bellwood420/pong-arcade-fpga/boards/DE10-NANO/reset_sync.sv

/*
 * Reset synchronizer (Intel/Altera)
 * Assert asynchronously, deassert synchronously
 */
module reset_sync(
  input   logic   clk,
  input   logic   reset,
  output  logic   out
);
  (* altera_attribute = {"-name SYNCHRONIZER_IDENTIFICATION FORCED_IF_ASYNCHRONOUS"} *) logic q1;
  (* altera_attribute = {"-name SYNCHRONIZER_IDENTIFICATION FORCED_IF_ASYNCHRONOUS"} *) logic q2;

  always @(posedge clk, posedge reset) begin
    if (reset) begin
      q1 <= 1'b1;
      q2 <= 1'b1;
    end else begin
      q1 <= 1'b0;
      q2 <= q1;
    end
  end

  assign out = q2;

endmodule
