bellwood420/pong-arcade-fpga/boards/NEXYS4DDR/NEXYS4DDR.srcs/sources_1/ip/mmcm/mmcm_stub.v

// Copyright 1986-2020 Xilinx, Inc. All Rights Reserved.
// --------------------------------------------------------------------------------
// Tool Version: Vivado v.2020.1 (win64) Build 2902540 Wed May 27 19:54:49 MDT 2020
// Date        : Sat Nov 14 17:16:30 2020
// Host        : DESKTOP running 64-bit major release  (build 9200)
// Command     : write_verilog -force -mode synth_stub -rename_top mmcm -prefix
//               mmcm_ mmcm_stub.v
// Design      : mmcm
// Purpose     : Stub declaration of top-level module interface
// Device      : xc7a100tcsg324-1
// --------------------------------------------------------------------------------

// This empty module with port declaration file causes synthesis tools to infer a black box for IP.
// The synthesis directives are for Synopsys Synplify support to prevent IO buffer insertion.
// Please paste the declaration into a Verilog source file or add the file as an additional source.
module mmcm(clk_out1, reset, clk_in1)
/* synthesis syn_black_box black_box_pad_pin="clk_out1,reset,clk_in1" */;
  output clk_out1;
  input reset;
  input clk_in1;
endmodule
