bellwood420/pong-arcade-fpga/boards/NEXYS4DDR/NEXYS4DDR.srcs/sources_1/ip/mmcm/mmcm_stub.vhdl

-- Copyright 1986-2020 Xilinx, Inc. All Rights Reserved.
-- --------------------------------------------------------------------------------
-- Tool Version: Vivado v.2020.1 (win64) Build 2902540 Wed May 27 19:54:49 MDT 2020
-- Date        : Sat Nov 14 17:16:30 2020
-- Host        : DESKTOP running 64-bit major release  (build 9200)
-- Command     : write_vhdl -force -mode synth_stub -rename_top mmcm -prefix
--               mmcm_ mmcm_stub.vhdl
-- Design      : mmcm
-- Purpose     : Stub declaration of top-level module interface
-- Device      : xc7a100tcsg324-1
-- --------------------------------------------------------------------------------
library IEEE;
use IEEE.STD_LOGIC_1164.ALL;

entity mmcm is
  Port ( 
    clk_out1 : out STD_LOGIC;
    reset : in STD_LOGIC;
    clk_in1 : in STD_LOGIC
  );

end mmcm;

architecture stub of mmcm is
attribute syn_black_box : boolean;
attribute black_box_pad_pin : string;
attribute syn_black_box of stub : architecture is true;
attribute black_box_pad_pin of stub : architecture is "clk_out1,reset,clk_in1";
begin
end;
